jsr606/cloudArray/hardware and documentation/PCB module schematics.png

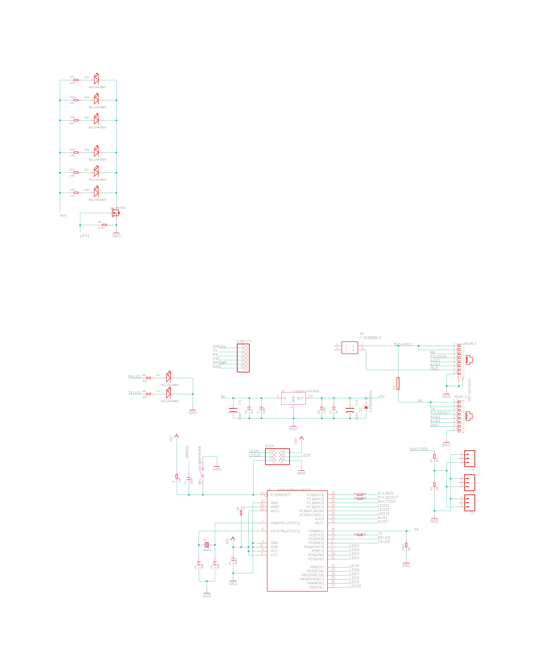
hardware and documentation/PCB module schematics.png
