jsr606/cloudArray/hardware and documentation/isometric assembly.png

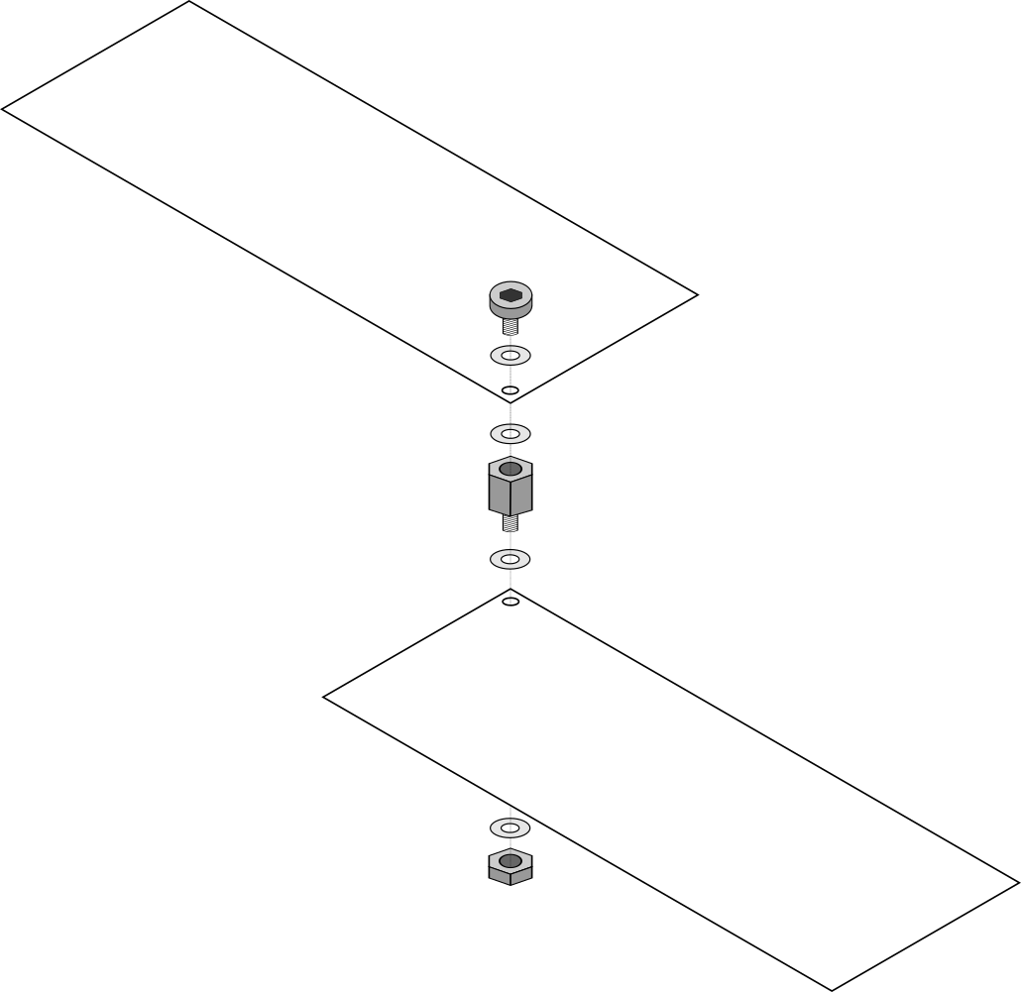
hardware and documentation/isometric assembly.png
